unjulee/sensor_dev/drawings/Hinges/double_hinge.png

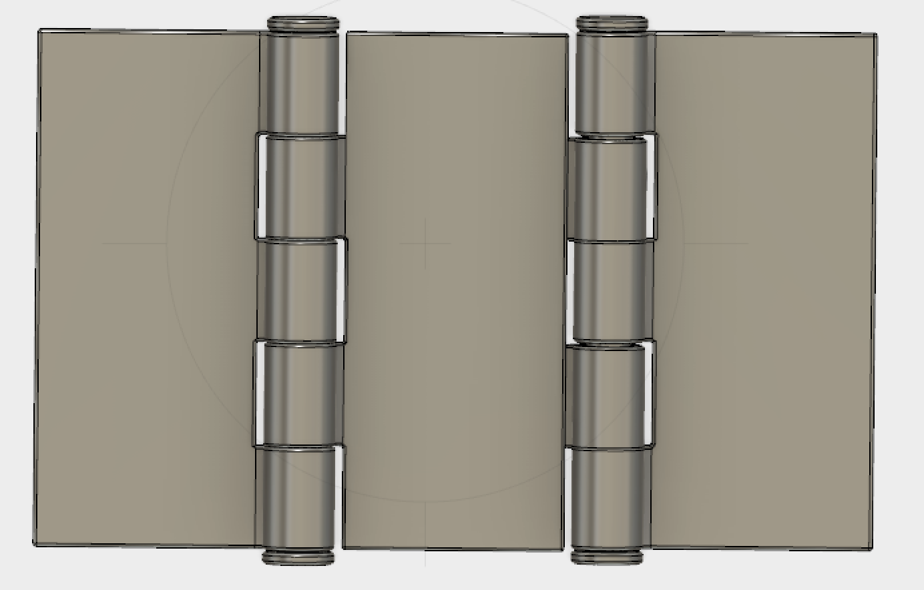
drawings/Hinges/double_hinge.png
