unjulee/sensor_dev/drawings/MAPE v6.png

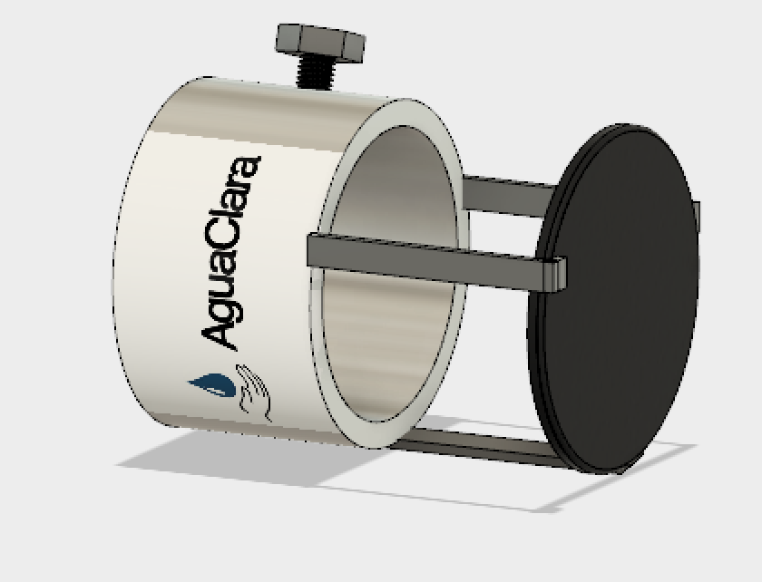
drawings/MAPE v6.png
