unjulee/sensor_dev/drawings/MAPE_2018-Mar-10_11-59-06PM-000_CustomizedView19818279152.png

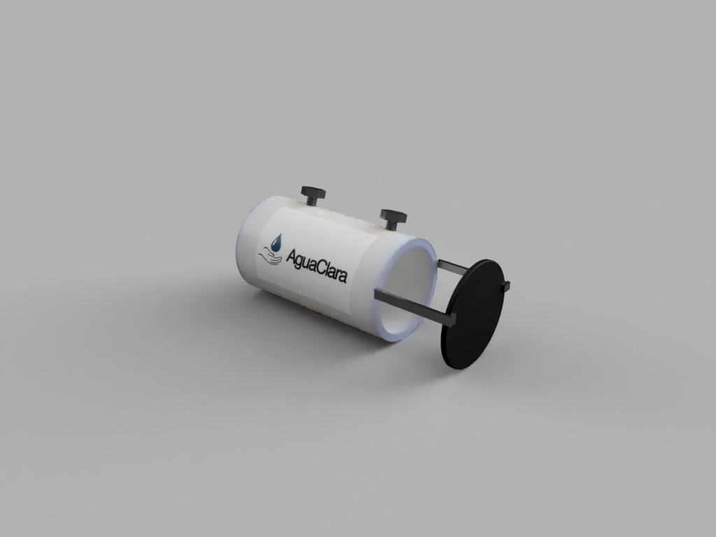
drawings/MAPE_2018-Mar-10_11-59-06PM-000_CustomizedView19818279152.png
