unjulee/sensor_dev/drawings/MAPE_extension_closeup.png

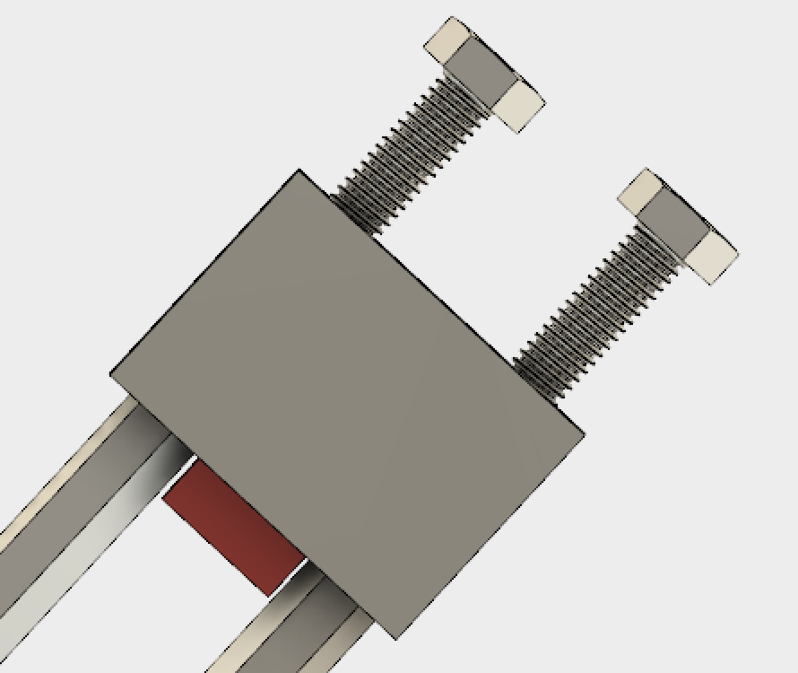
drawings/MAPE_extension_closeup.png
