unjulee/sensor_dev/drawings/MAPE_extension_full.png

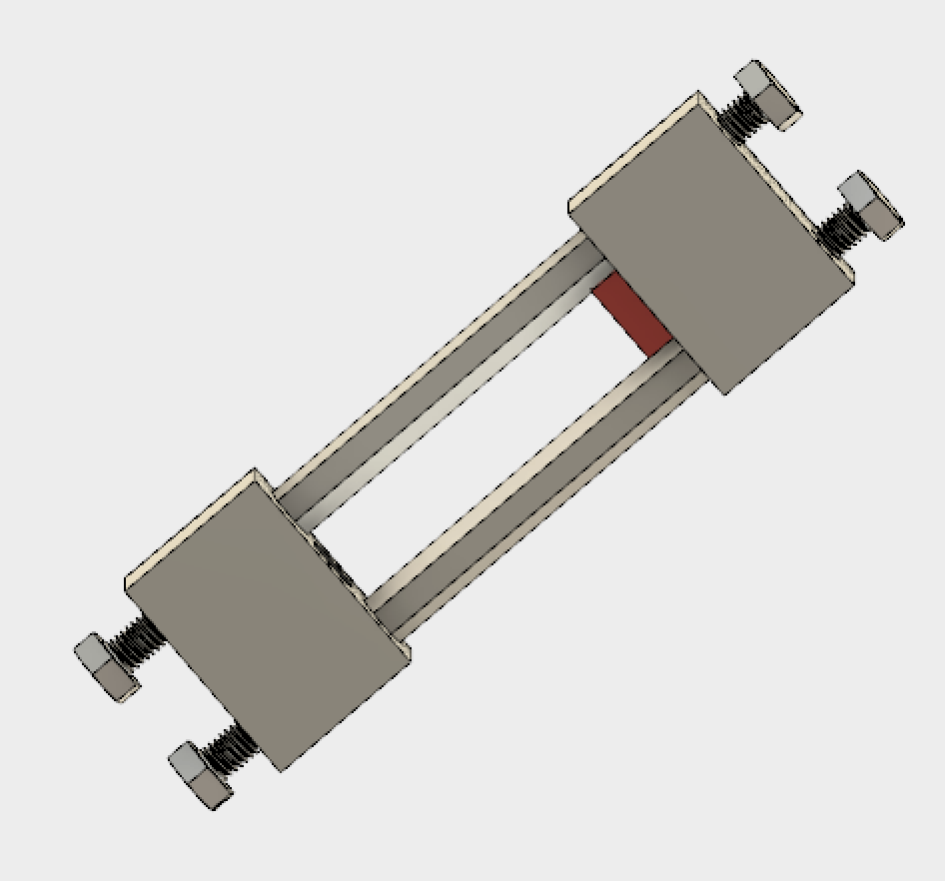
drawings/MAPE_extension_full.png
