unjulee/sensor_dev/images/MIA_whole.jpg

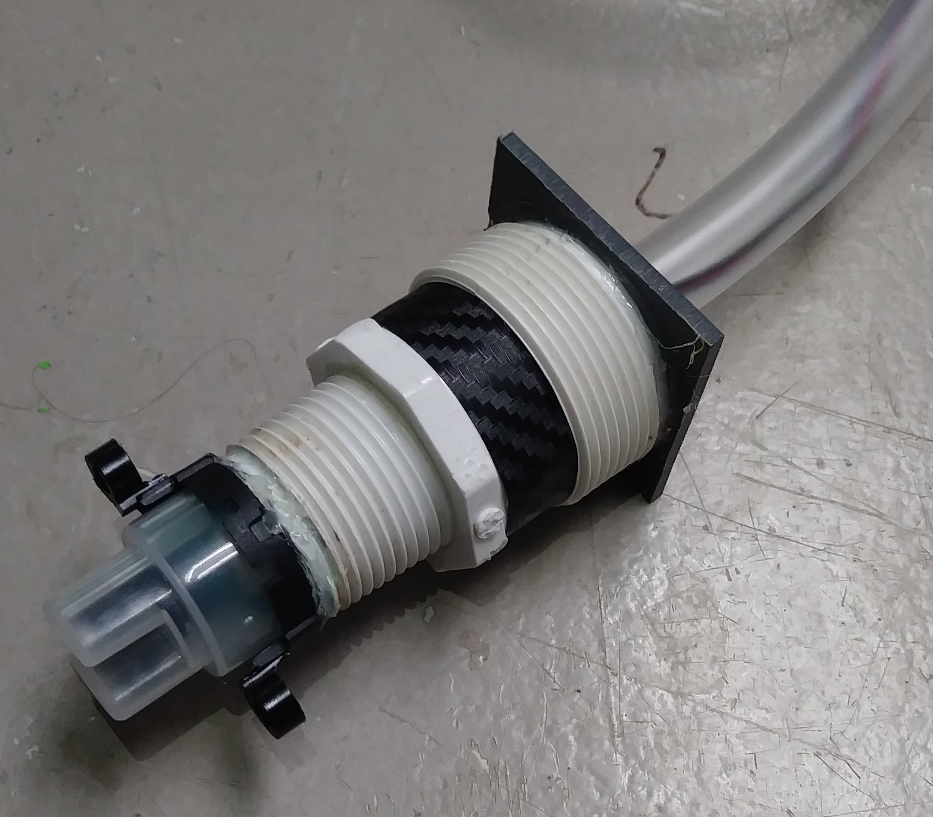
images/MIA_whole.jpg
