unjulee/sensor_dev/images/ruler1.jpg

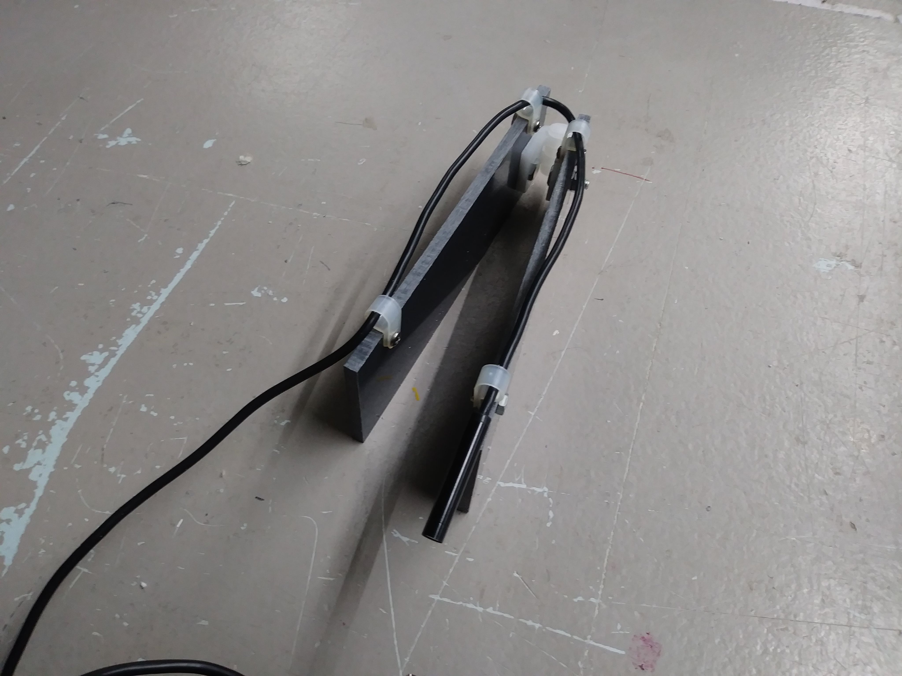
images/ruler1.jpg
