unjulee/sensor_dev/images/ruler3.jpg

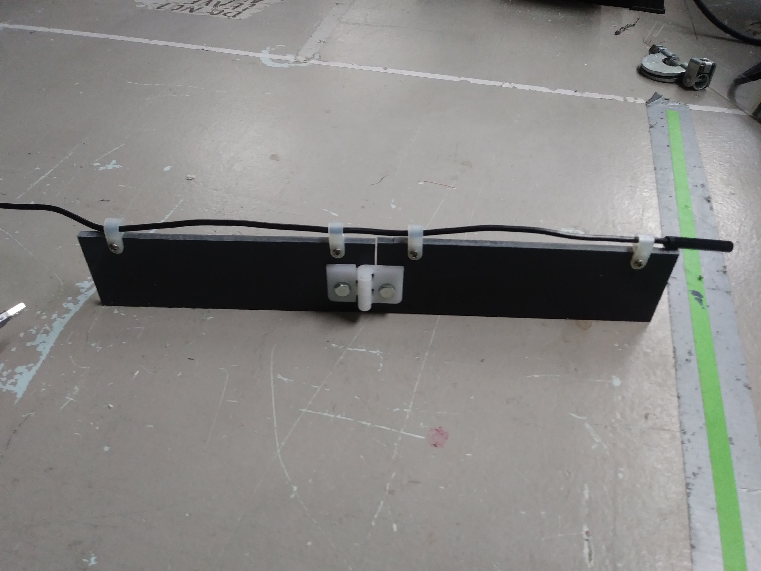
images/ruler3.jpg
