unjulee/sensor_dev/logs/week2/model.jpg

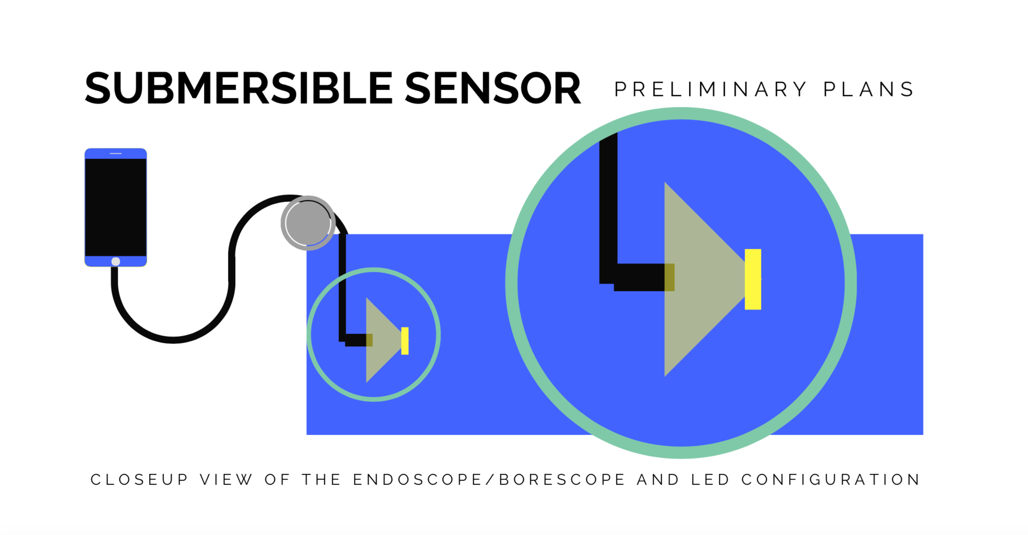
logs/week2/model.jpg
